Tsar/smart_home/dimmer_micros_adjustment.png

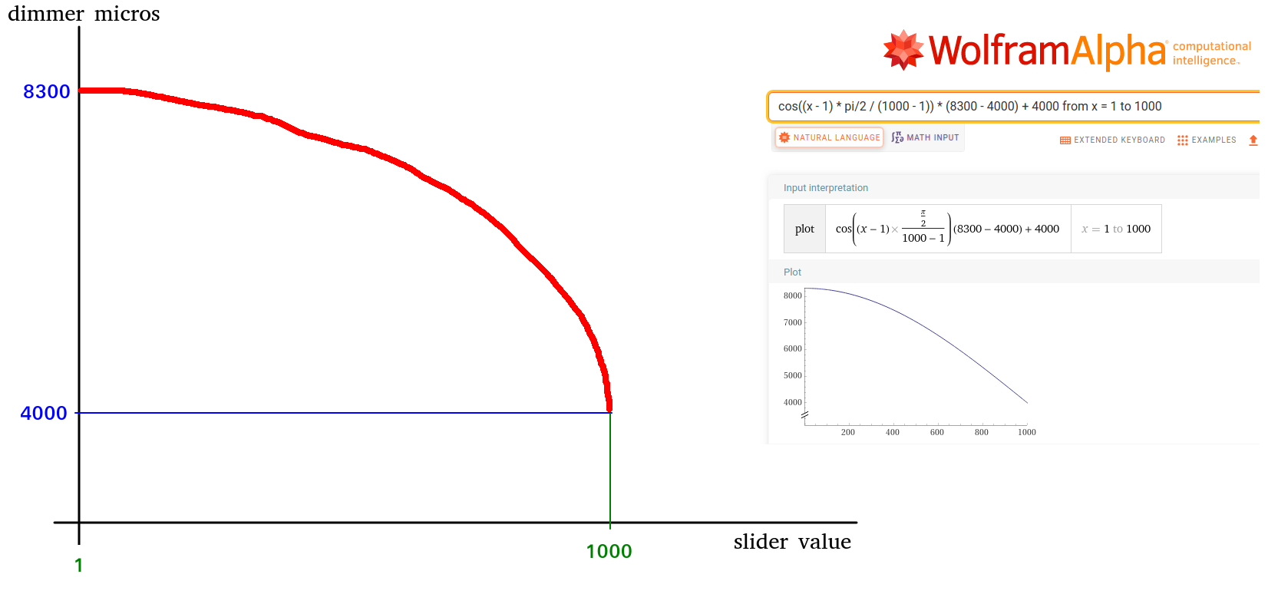
dimmer_micros_adjustment.png
