Tsar/smart_home/Sprint_Layout_and_other_engineering_stuff/Smart_Home_Foto_Screenshots_Specs/210711_Тепловыдел_Резисторов_15к_Блок_Меандр.jpg

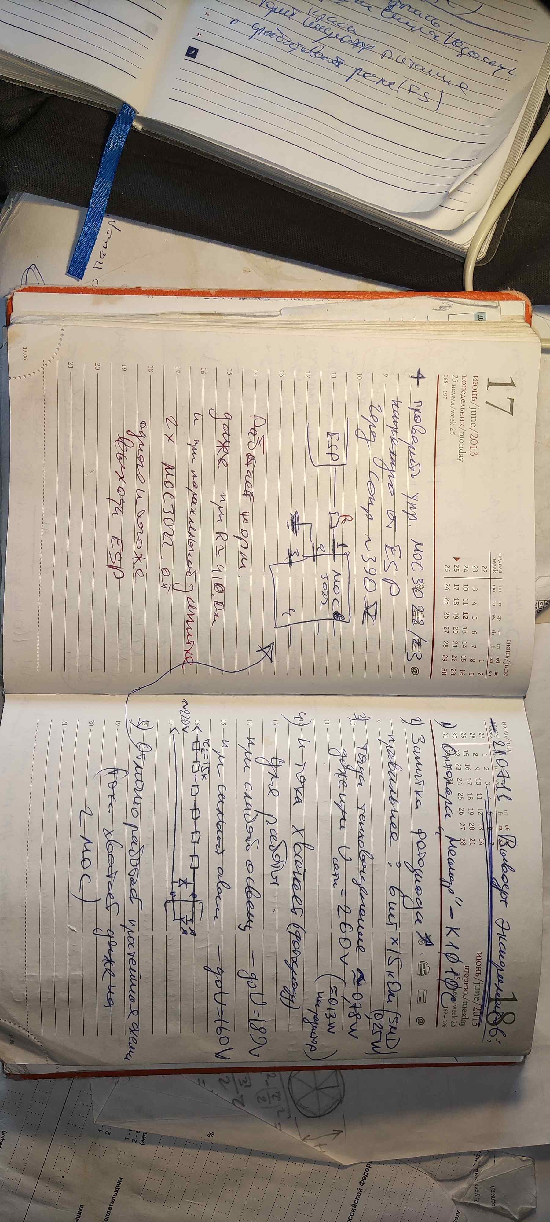
Sprint_Layout_and_other_engineering_stuff/Smart_Home_Foto_Screenshots_Specs/210711_Тепловыдел_Резисторов_15к_Блок_Меандр.jpg
