Tsar/smart_home/Sprint_Layout_and_other_engineering_stuff/Smart_Home_Foto_Screenshots_Specs/210718_Идея контактн держателя для прошивки ESP8266.jpg

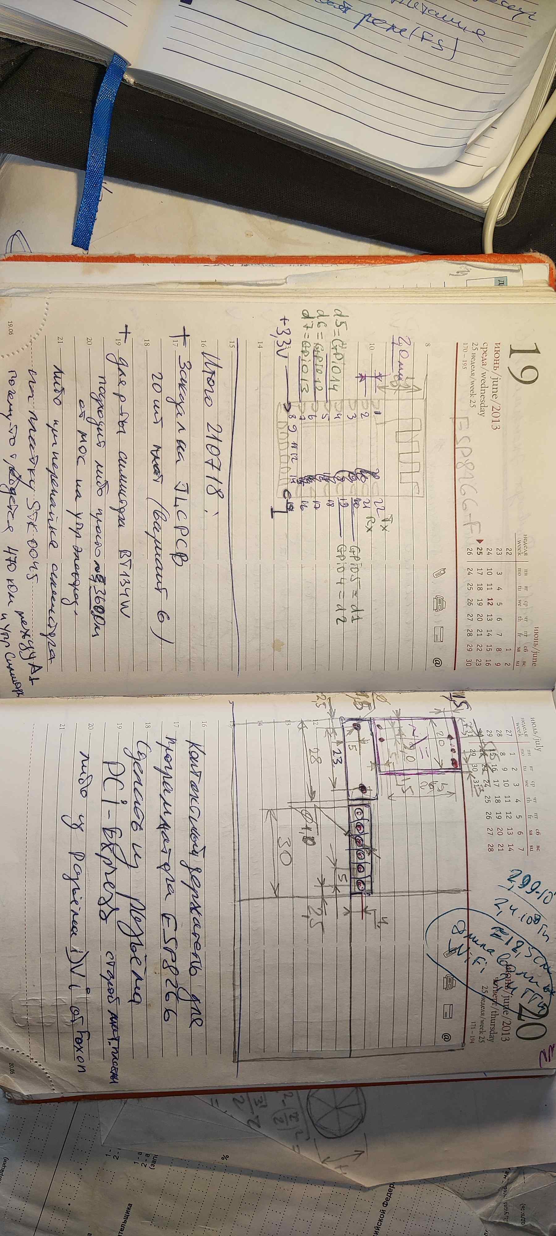
Sprint_Layout_and_other_engineering_stuff/Smart_Home_Foto_Screenshots_Specs/210718_Идея контактн держателя для прошивки ESP8266.jpg
