Tsar/smart_home/Sprint_Layout_and_other_engineering_stuff/Smart_Home_Foto_Screenshots_Specs/210820_тест разн ламп на стенде Смарт Хоум.jpg

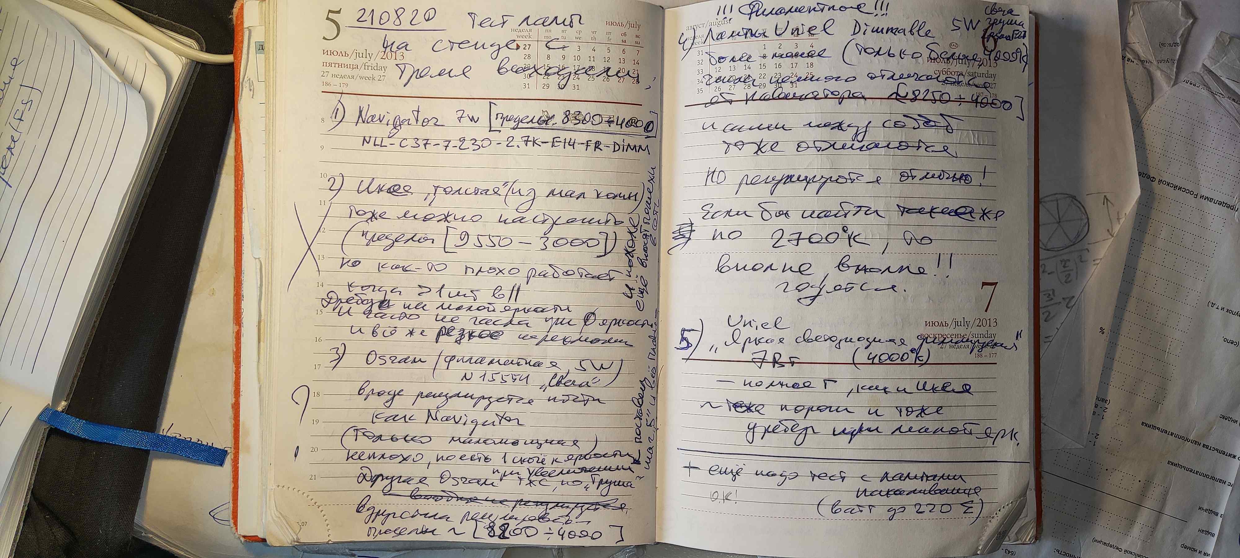
Sprint_Layout_and_other_engineering_stuff/Smart_Home_Foto_Screenshots_Specs/210820_тест разн ламп на стенде Смарт Хоум.jpg
