Tsar/smart_home/Sprint_Layout_and_other_engineering_stuff/Smart_Home_Foto_Screenshots_Specs/210923_Блок-схема Смарт-Хоум_тжс.jpg

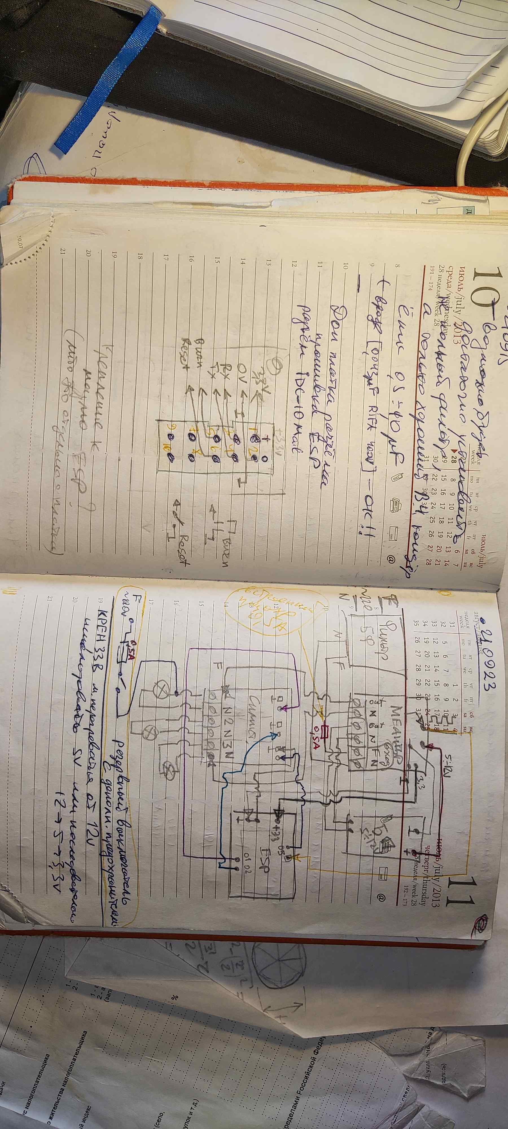
Sprint_Layout_and_other_engineering_stuff/Smart_Home_Foto_Screenshots_Specs/210923_Блок-схема Смарт-Хоум_тжс.jpg
