Tsar/smart_home/Sprint_Layout_and_other_engineering_stuff/Smart_Home_Foto_Screenshots_Specs/Smart_Home_Схема_наш_Смарт-Хоум 2021.jpg

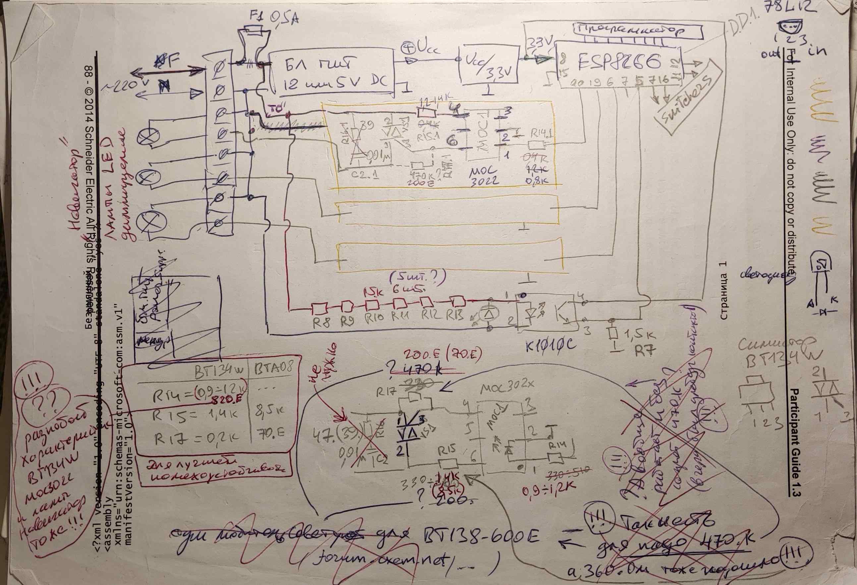
Sprint_Layout_and_other_engineering_stuff/Smart_Home_Foto_Screenshots_Specs/Smart_Home_Схема_наш_Смарт-Хоум 2021.jpg
