Tsar/smart_home/Sprint_Layout_and_other_engineering_stuff/Smart_Home_Foto_Screenshots_Specs/Осциллограммы_Морганий_Ламп_210912.png

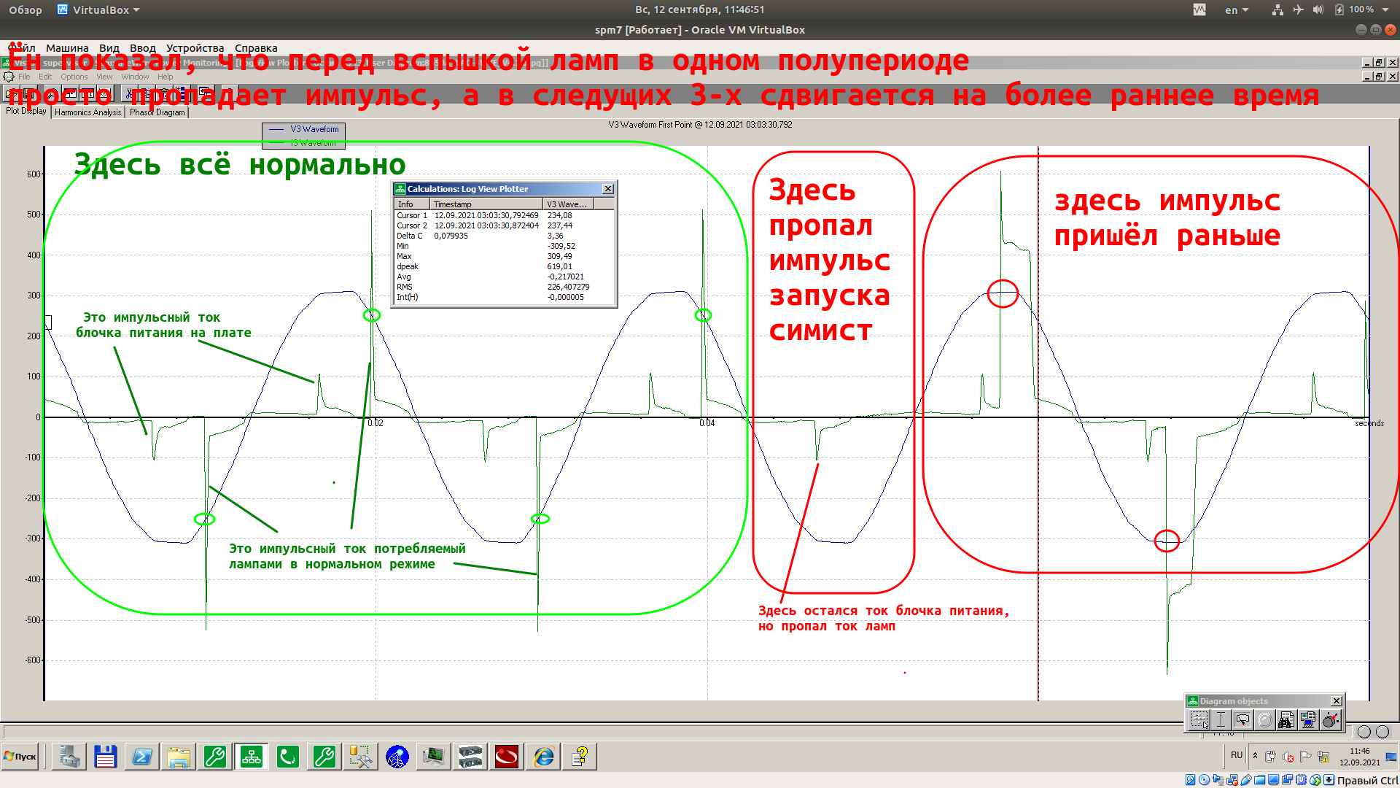
Sprint_Layout_and_other_engineering_stuff/Smart_Home_Foto_Screenshots_Specs/Осциллограммы_Морганий_Ламп_210912.png
