Tsar/smart_home/Sprint_Layout_and_other_engineering_stuff/Smart_Home_Foto_Screenshots_Specs/Пик ток 8 А Не димм лампа 7 W E27.png

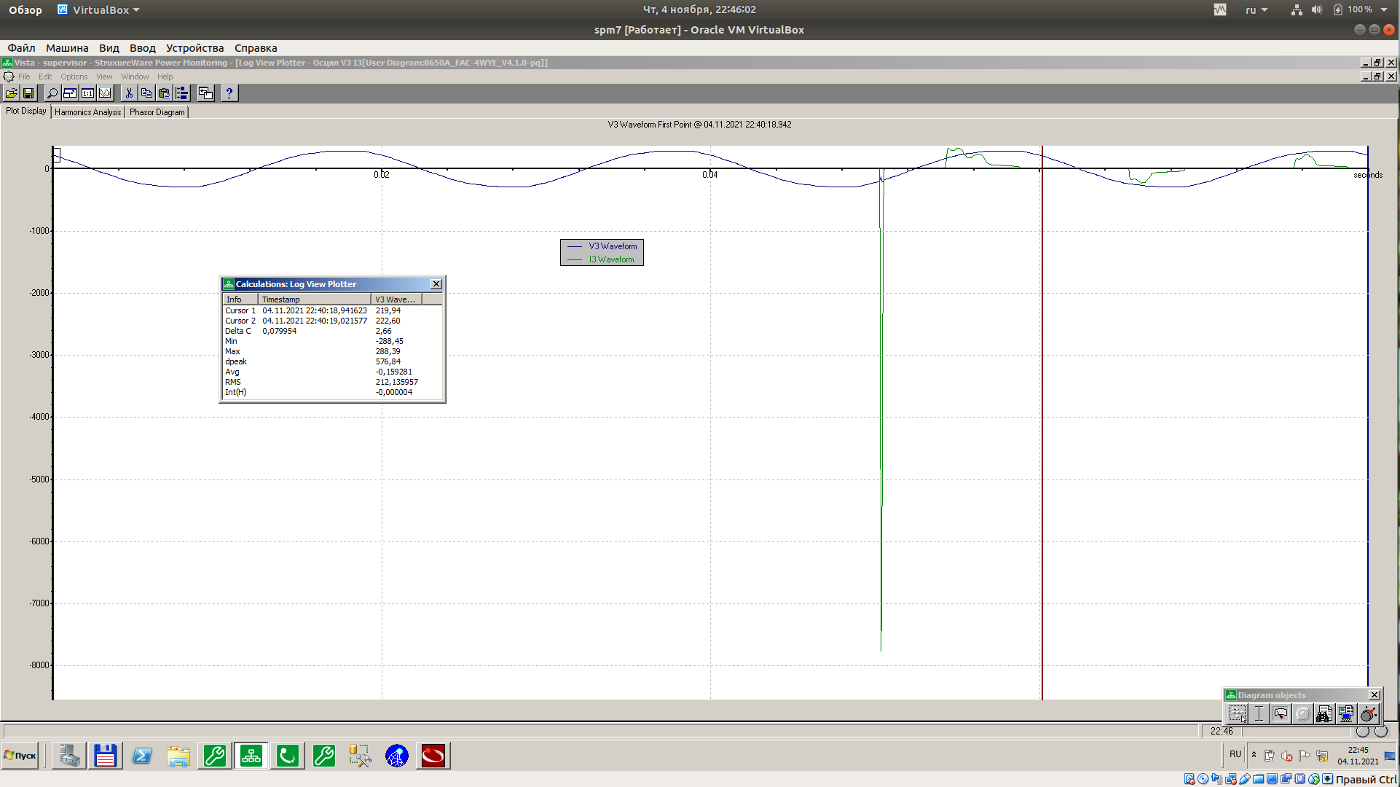
Sprint_Layout_and_other_engineering_stuff/Smart_Home_Foto_Screenshots_Specs/Пик ток 8 А Не димм лампа 7 W E27.png
