Tsar/smart_home/Sprint_Layout_and_other_engineering_stuff/Smart_Home_Foto_Screenshots_Specs/Пик ток 11 А Не димм лампа 10 W E27.png

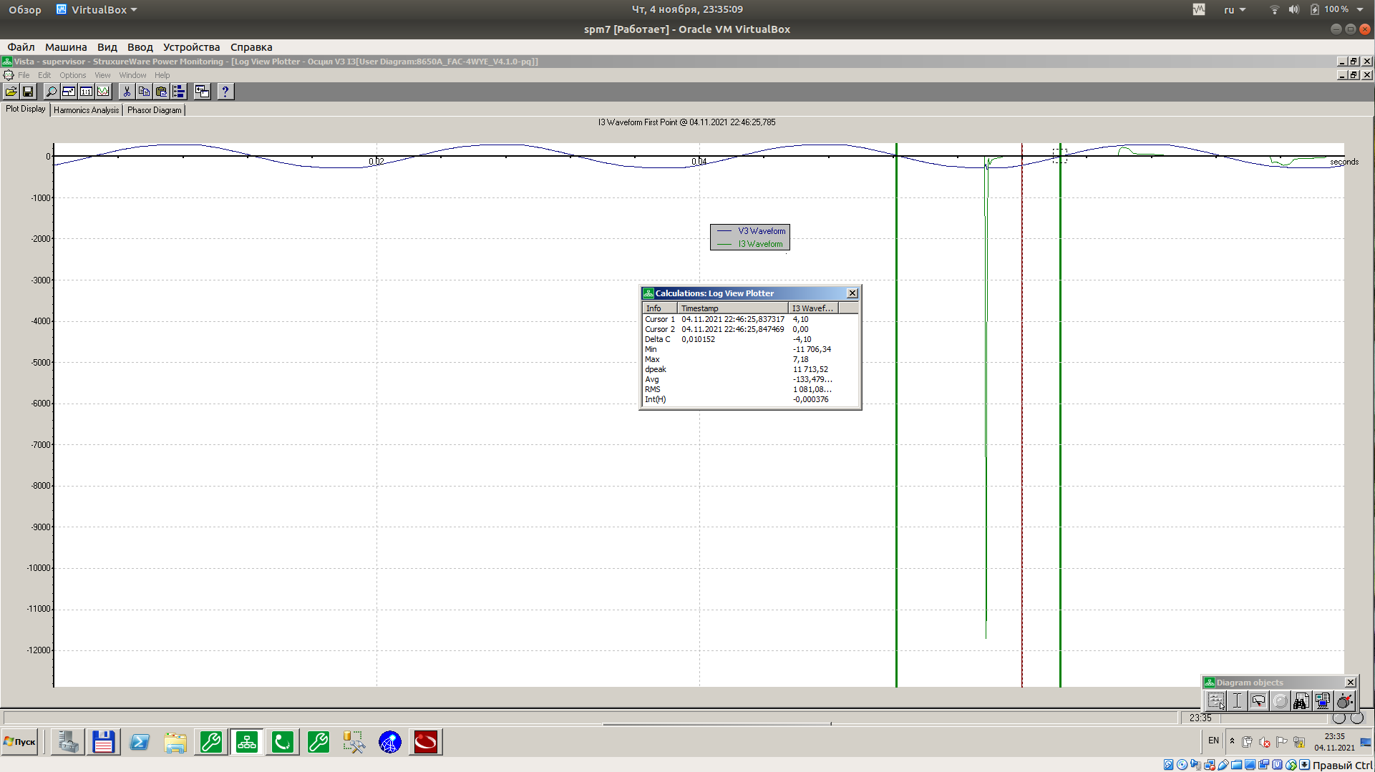
Sprint_Layout_and_other_engineering_stuff/Smart_Home_Foto_Screenshots_Specs/Пик ток 11 А Не димм лампа 10 W E27.png
