Tsar/smart_home/Sprint_Layout_and_other_engineering_stuff/Smart_Home_Foto_Screenshots_Specs/Пик ток 29мА димм лампа Юниел 5 W.png

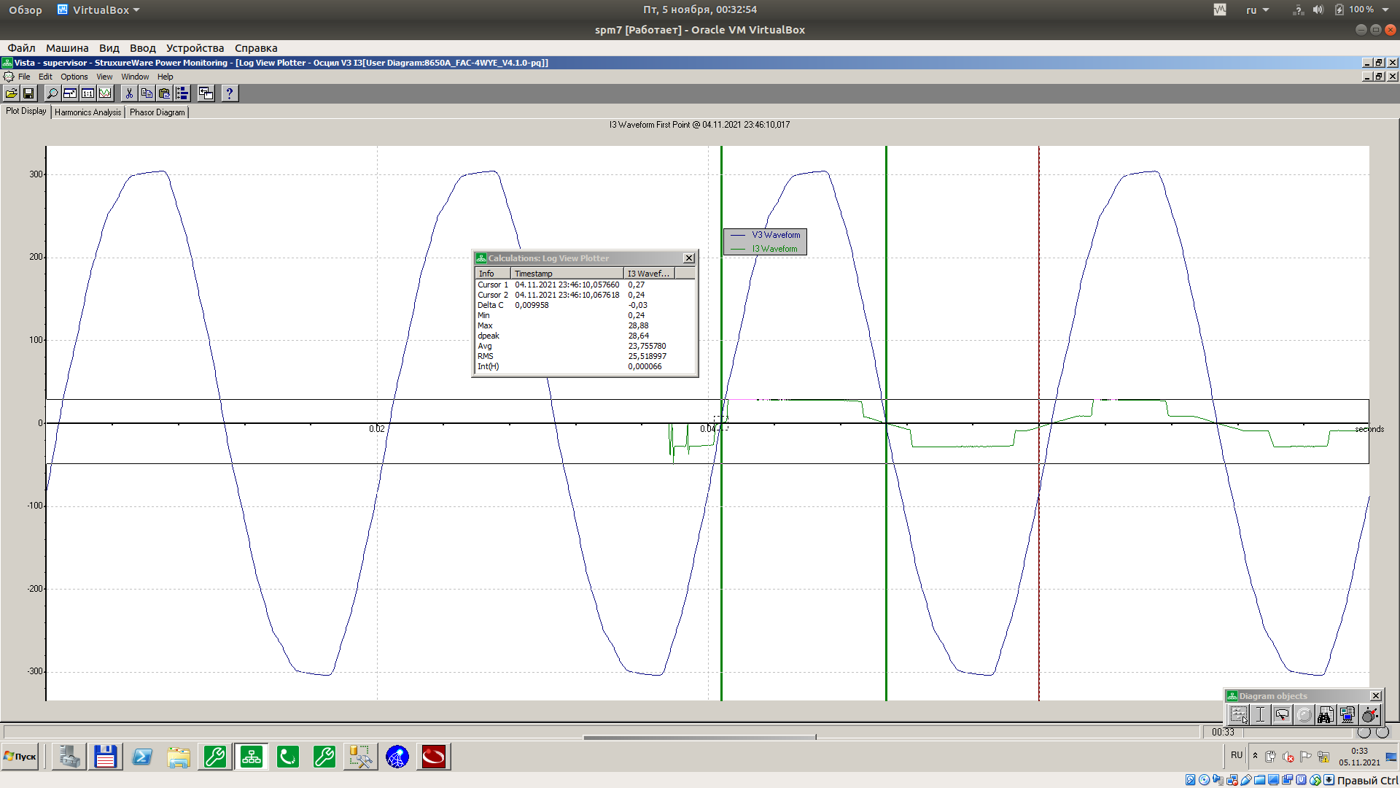
Sprint_Layout_and_other_engineering_stuff/Smart_Home_Foto_Screenshots_Specs/Пик ток 29мА димм лампа Юниел 5 W.png
