Tsar/smart_home/Sprint_Layout_and_other_engineering_stuff/Smart_Home_Foto_Screenshots_Specs/Пик ток 37мА димм лампа Ферон 7 W.png

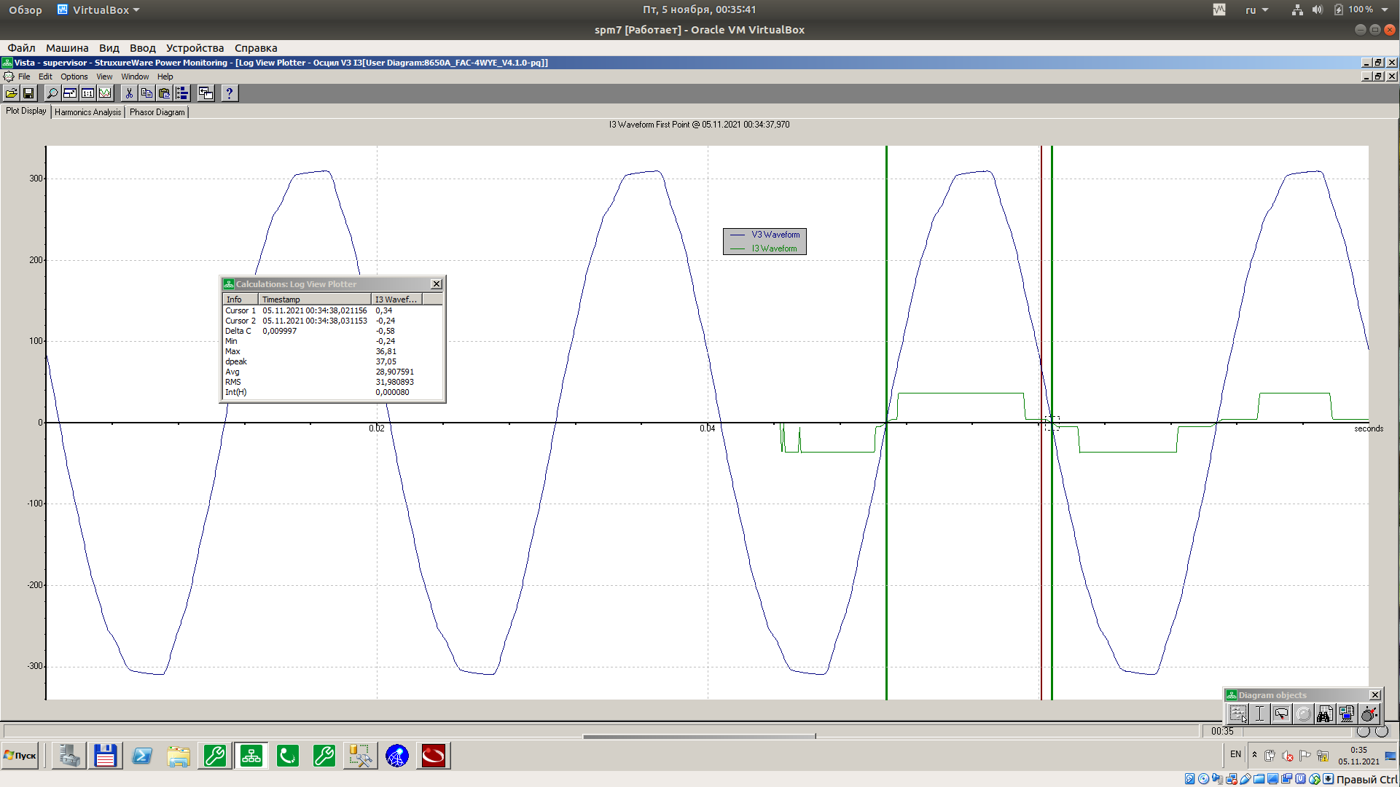
Sprint_Layout_and_other_engineering_stuff/Smart_Home_Foto_Screenshots_Specs/Пик ток 37мА димм лампа Ферон 7 W.png
