Tsar/smart_home/Sprint_Layout_and_other_engineering_stuff/SprintLayout_main_projects_and_gerber-files_Smart_Home/019_ESP8266_+Meandr+Simist.lay6.png

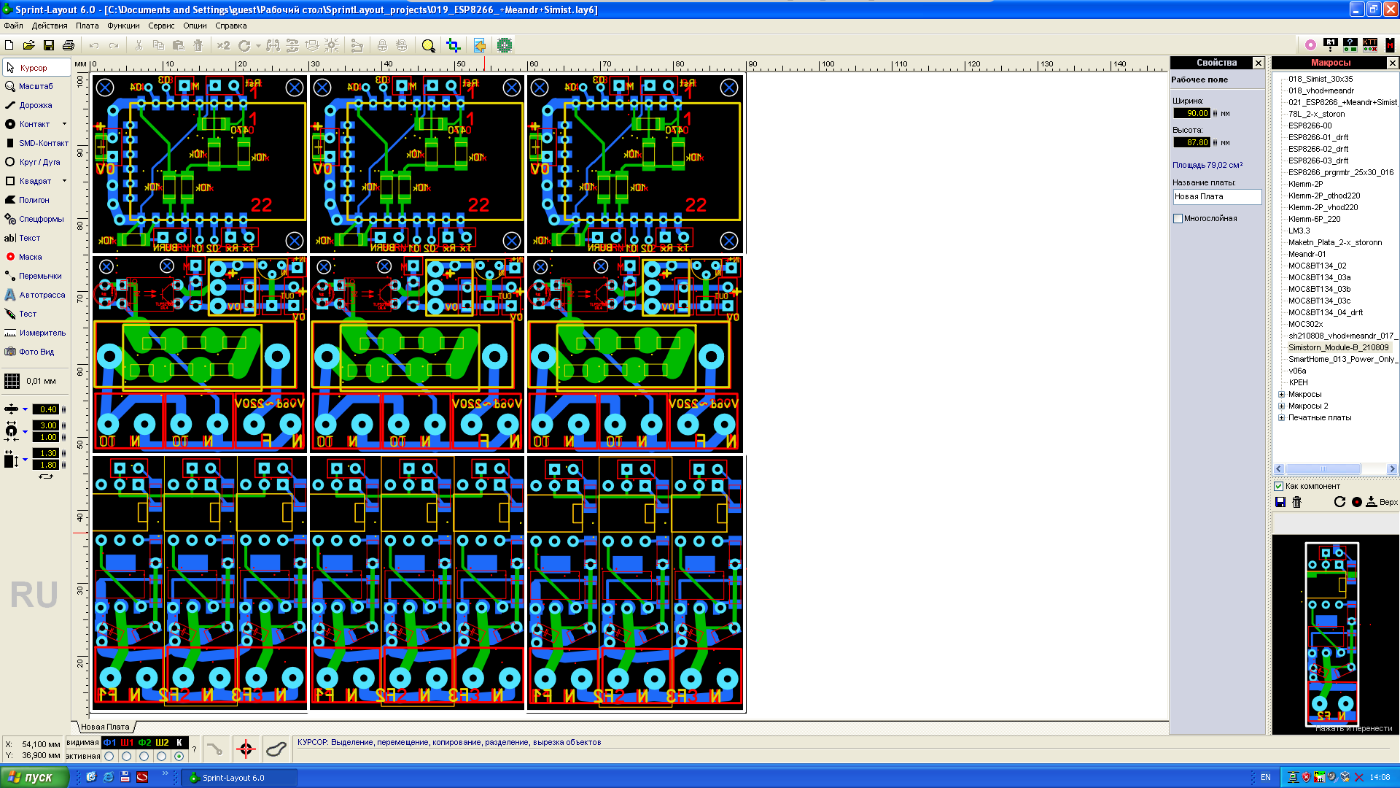
Sprint_Layout_and_other_engineering_stuff/SprintLayout_main_projects_and_gerber-files_Smart_Home/019_ESP8266_+Meandr+Simist.lay6.png
