Tsar/smart_home/Sprint_Layout_and_other_engineering_stuff/Smart_Home_Foto_Screenshots_Specs/Variant_05_Maket_SmartHome_IMG_20210619_194450.jpg

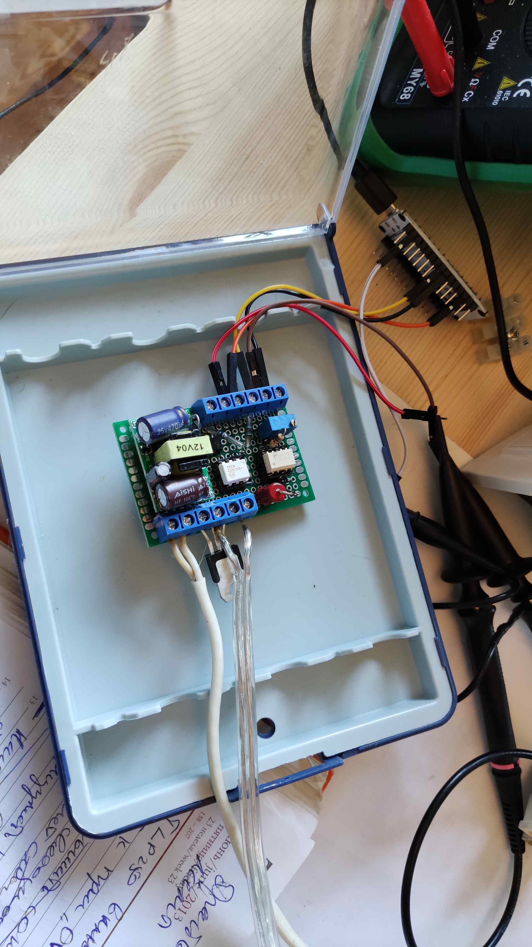
Sprint_Layout_and_other_engineering_stuff/Smart_Home_Foto_Screenshots_Specs/Variant_05_Maket_SmartHome_IMG_20210619_194450.jpg
