Tsar/smart_home/Sprint_Layout_and_other_engineering_stuff/Tests_Results_and_plans/лампа Navigator 7W 2700K E14 NLL-C37-7-230-2.7K-E14-3STEPDIMM.png

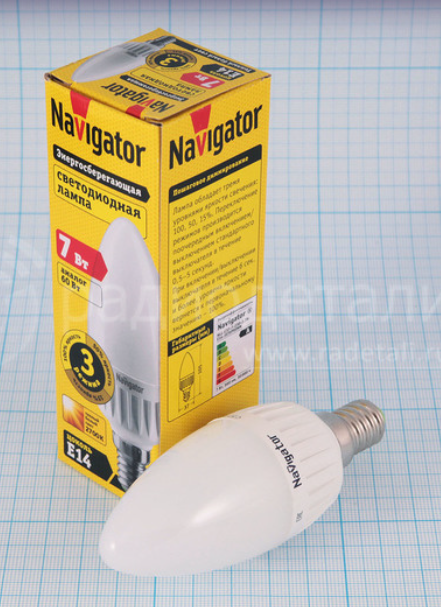
Sprint_Layout_and_other_engineering_stuff/Tests_Results_and_plans/лампа Navigator 7W 2700K E14 NLL-C37-7-230-2.7K-E14-3STEPDIMM.png
