Tsar/smart_home/Sprint_Layout_and_other_engineering_stuff/Tests_Results_and_plans/Лампа Navigator 10W 2700K E27 NLL-A60-10-230-2.7K-E27-DIMM .png

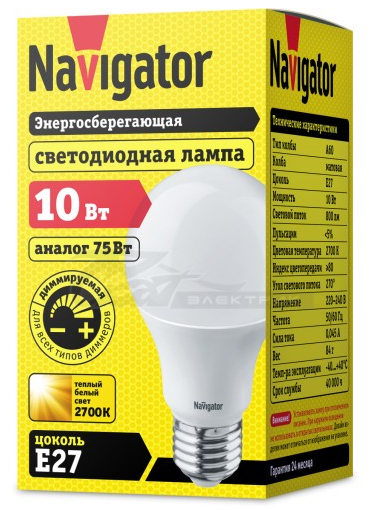
Sprint_Layout_and_other_engineering_stuff/Tests_Results_and_plans/Лампа Navigator 10W 2700K E27 NLL-A60-10-230-2.7K-E27-DIMM .png
